NightHawk32/ESP32-Multi-ePaper-Clock/01_src/res/6.png

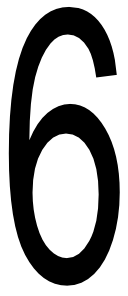
01_src/res/6.png
